Cpt-Quantum/UV_Exposure_Unit/debounce.h

/* Microchip Technology Inc. and its subsidiaries.  You may use this software 
 * and any derivatives exclusively with Microchip products. 
 * 
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
 * IN NO EVENT WILL MICROCHIP BE LIABLE FOR ANY INDIRECT, SPECIAL, PUNITIVE, 
 * INCIDENTAL OR CONSEQUENTIAL LOSS, DAMAGE, COST OR EXPENSE OF ANY KIND 
 * WHATSOEVER RELATED TO THE SOFTWARE, HOWEVER CAUSED, EVEN IF MICROCHIP HAS 
 * BEEN ADVISED OF THE POSSIBILITY OR THE DAMAGES ARE FORESEEABLE.  TO THE 
 * FULLEST EXTENT ALLOWED BY LAW, MICROCHIP'S TOTAL LIABILITY ON ALL CLAIMS 
 * IN ANY WAY RELATED TO THIS SOFTWARE WILL NOT EXCEED THE AMOUNT OF FEES, IF 
 * ANY, THAT YOU HAVE PAID DIRECTLY TO MICROCHIP FOR THIS SOFTWARE.
 *
 * MICROCHIP PROVIDES THIS SOFTWARE CONDITIONALLY UPON YOUR ACCEPTANCE OF THESE 
 * TERMS. 
 */

/* 
 * File:   
 * Author: 
 * Comments:
 * Revision history: 
 */

// This is a guard condition so that contents of this file are not included
// more than once.  
#ifndef debounce
#define	debounce

#include <stdint.h>

//Prototype function declarations
//Debounce and latching function for each button
void debounce_ON_BTN();
void debounce_TOP_BTN();
void debounce_BOTTOM_BTN();
void debounce_TMR_DOWN_BTN();
void debounce_TMR_UP_BTN();
void debounce_TMR_SET_BTN();

//Initialisation function
void debounce_initialise();

//State accessing functions
uint8_t ON_State();
uint8_t TMR_SET_State();
uint8_t TOP_State();
uint8_t BOTTOM_State();

//Function to reset all states
void Reset_States();

//Function to return set on_time
unsigned long On_Time();

//Function to set the on time
void Set_On_Time(unsigned long set_on_time);

#endif
